tlalexander/rgb_led_earrings/parts/DWV0008A.stp

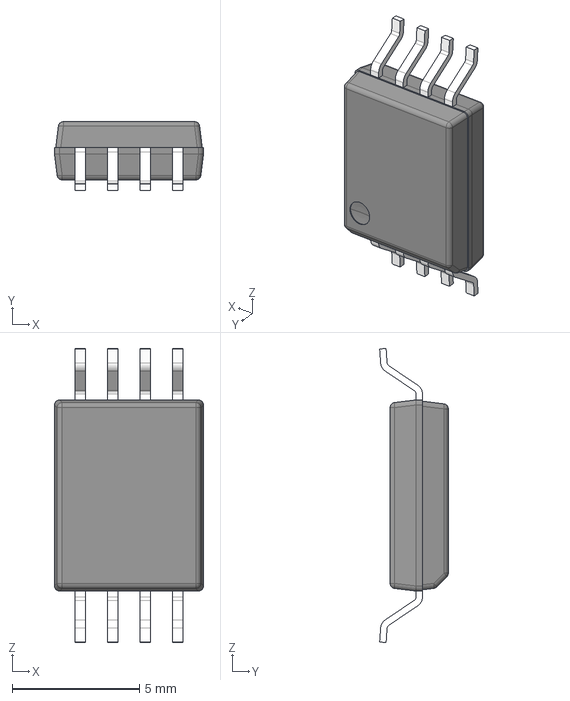
[picture p18: CAD file, 2024-02-05]
parts/DWV0008A.stp
5.85 x 2.70 x 11.5 mm
BODY-SOIC
LEAD-DWV0008A x 8
