tlalexander/rgb_led_earrings/parts/earring_pcb - Flat pattern of pcb.dxf

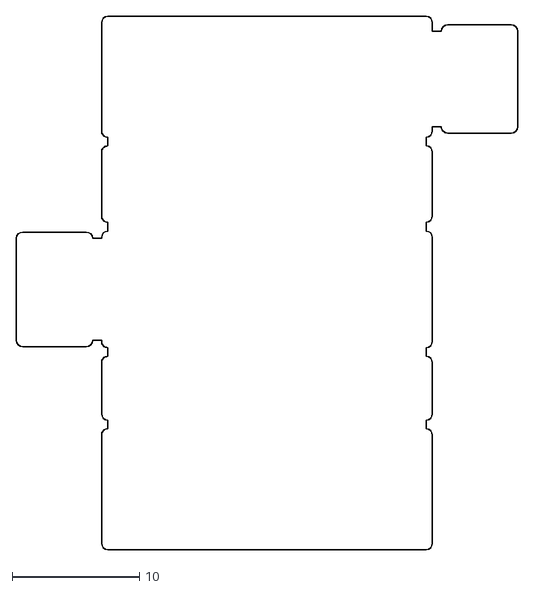
[picture p19: CAD file, 2024-02-05]
parts/earring_pcb - Flat pattern of pcb.dxf
39.4 x 41.9
