tlalexander/rgb_led_earrings/parts/USB4125-GF-A-0190--3DModel-STEP-56544.STEP

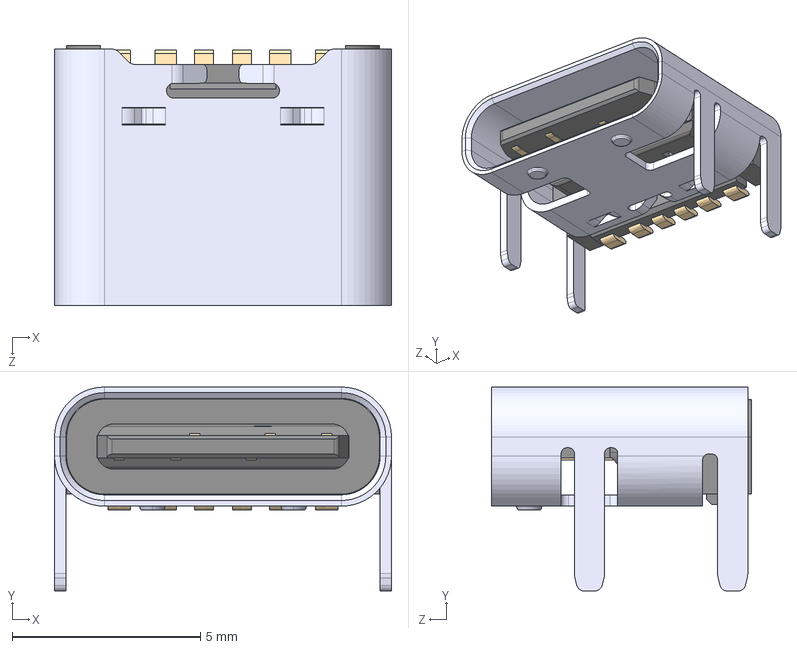
[picture p20: CAD file, 2024-02-05]
parts/USB4125-GF-A-0190--3DModel-STEP-56544.STEP
8.94 x 5.41 x 6.90 mm
