tlalexander/rgb_led_earrings/parts/USB-C-TH_GT-USB-7055.obj

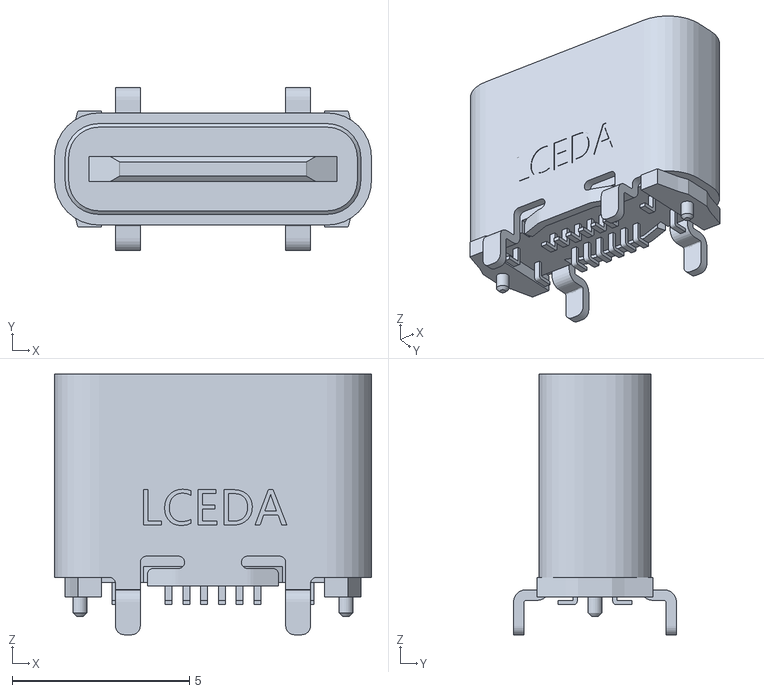
[picture p21: CAD file, 2024-02-05]
parts/USB-C-TH_GT-USB-7055.obj
8.94 x 4.60 x 7.35
