tlalexander/rgb_led_earrings/parts/WDFN-6-2x2.step

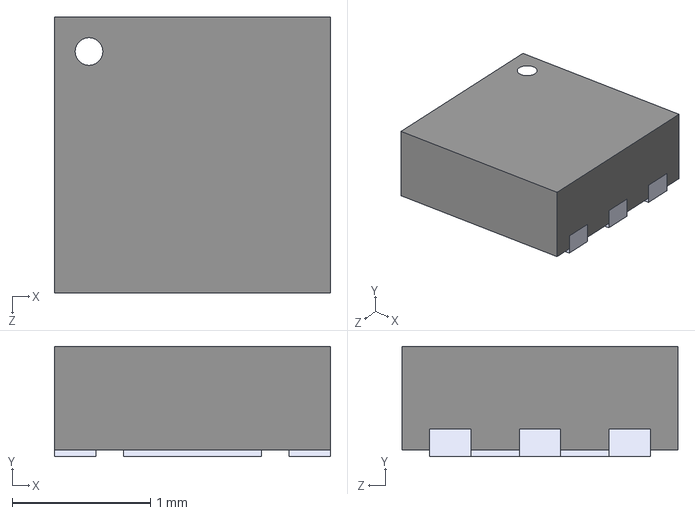
[picture p22: CAD file, 2024-02-05]
parts/WDFN-6-2x2.step
2.00 x 0.8 x 2.00 mm
